hb020/PoE_Ethernet_GPIB_Adapter/HW/DT/Figs/Eth_Clock.png

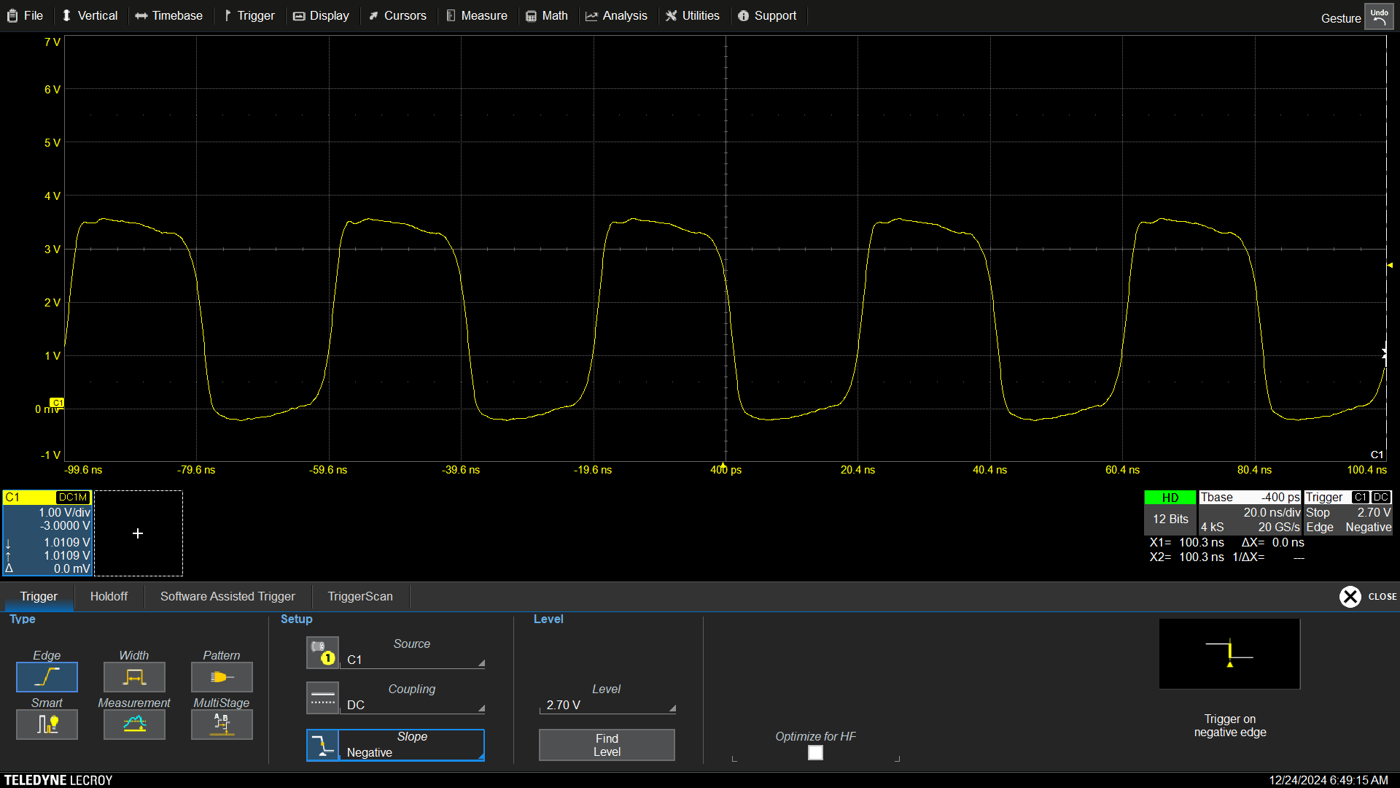
HW/DT/Figs/Eth_Clock.png
