hb020/PoE_Ethernet_GPIB_Adapter/HW/DT/Figs/MISO.png

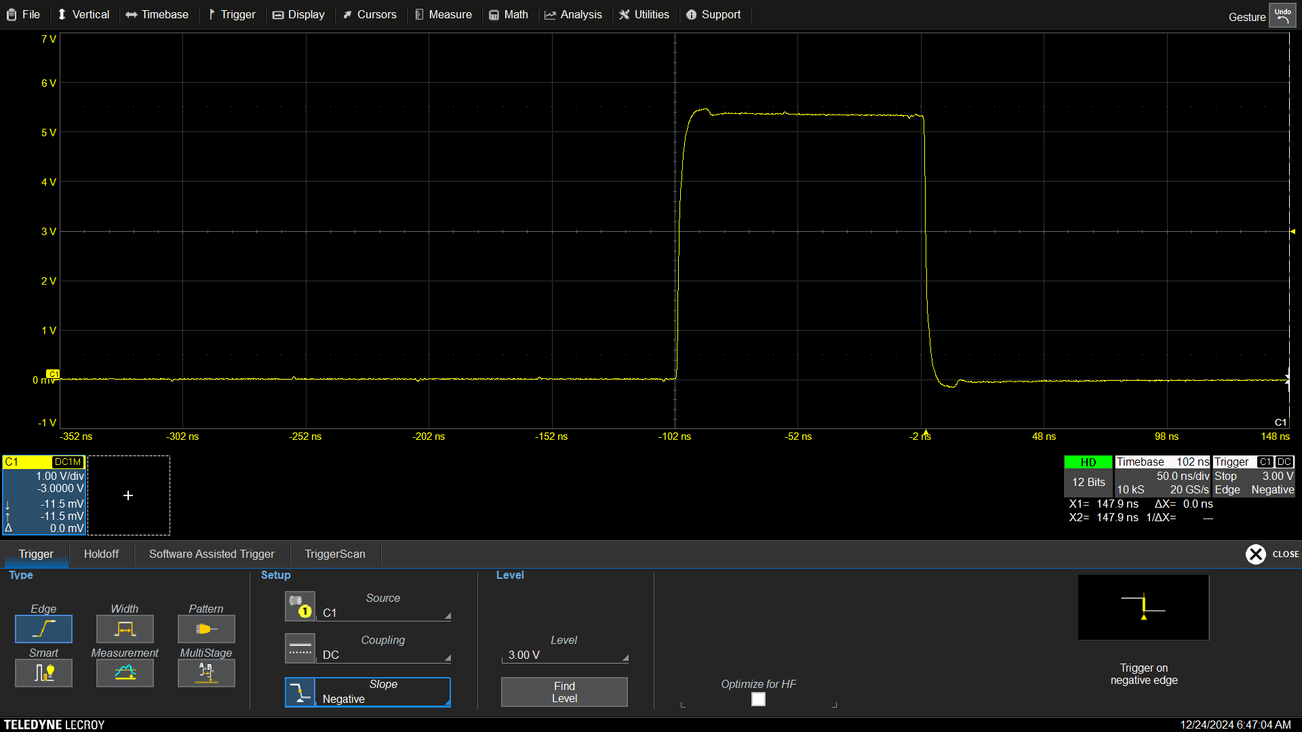
HW/DT/Figs/MISO.png
