hb020/PoE_Ethernet_GPIB_Adapter/HW/DT/Figs/MOSI_3v3.png

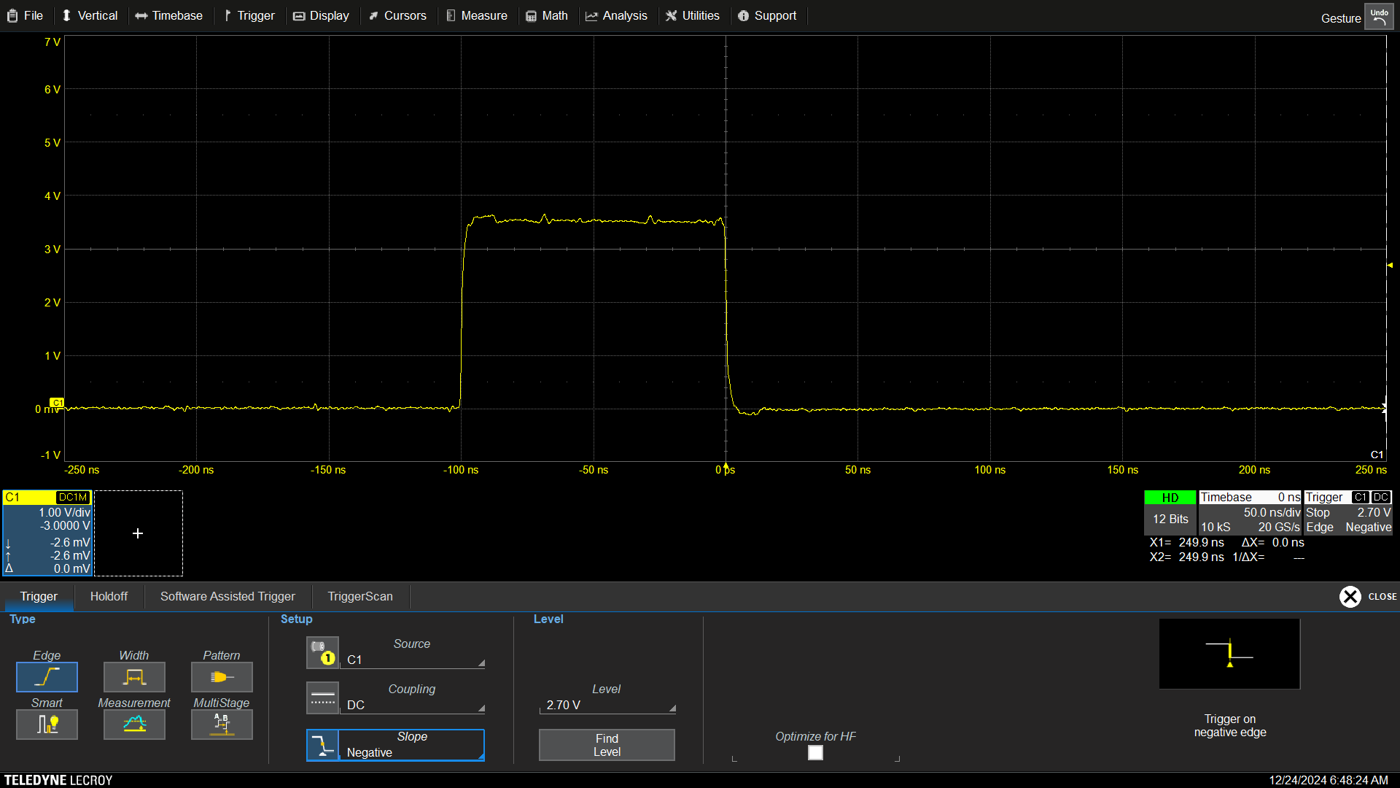
HW/DT/Figs/MOSI_3v3.png
