hb020/PoE_Ethernet_GPIB_Adapter/HW/DT/Figs/SCL.png

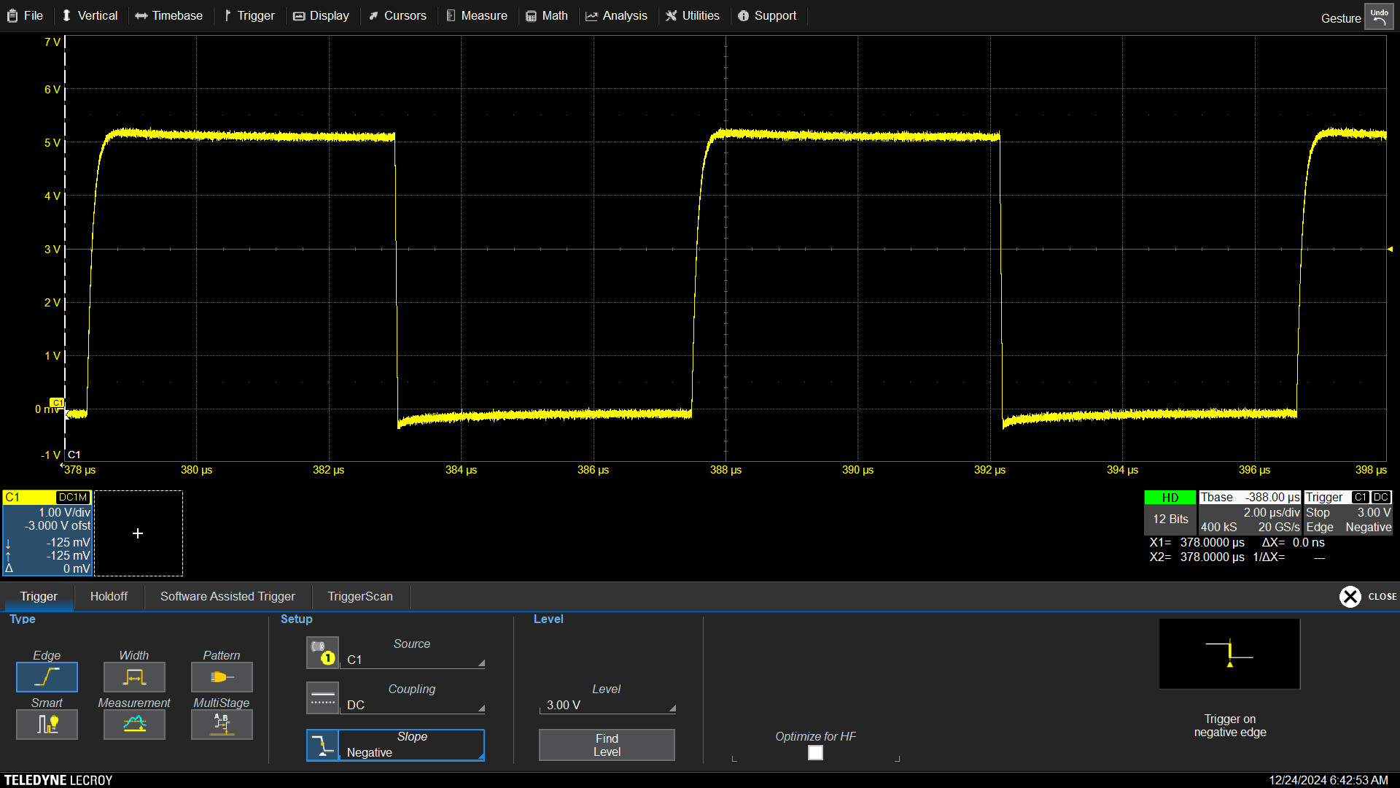
HW/DT/Figs/SCL.png
