hb020/PoE_Ethernet_GPIB_Adapter/HW/3d_models/155124M173200.step

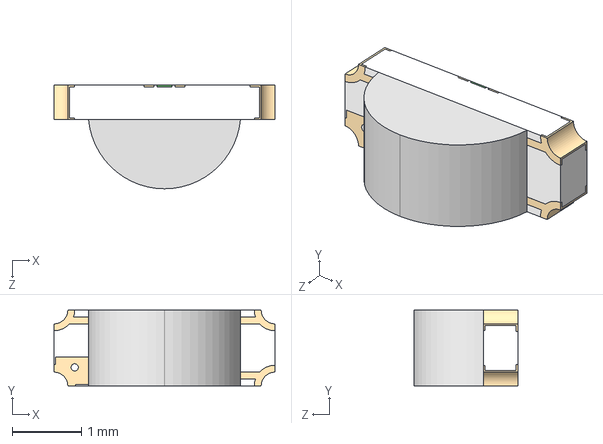
[picture p34: CAD file, 2024-12-25]
HW/3d_models/155124M173200.step
3.20 x 1.10 x 1.50 mm
